Ghost3379/NX-ISD/ISD-Core/src/pins.h

#pragma once

// I2C
#define I2C_SDA 8
#define I2C_SCL 9

// SPI
#define SPI_SCK 40
#define SPI_MISO 41
#define SPI_MOSI 42

// Display 
#define CS_TFT 48
#define TFT_RS 21
#define TFT_RST 38
#define TFT_PWM 1
#define CS_SD 47

// Power Control
#define PWR_NPM 17

// Peripherals
#define NPM 18
#define BUZZER 10

// Buttons
#define BTN 13
#define LEVER_LEFT 16
#define LEVER_PUSH 15
#define LEVER_RIGHT 14

// Interrupts
#define INT_ALS 39
#define INT_RTC 6
#define INT_HR 5
#define INT_DOF 2
#define ALERT 4

// Charging & USB Detection
#define USB_DETECT 12
#define BAT_STAT 11
