Ghost3379/NX-ISD/ISD-Core/src/Watchface.h

#pragma once
#include <Arduino.h>
#include <LovyanGFX.hpp>
#include "SensorState.h"
#include "HAL.h"
#include "storage/StorageManager.h"

enum AppView {
  VIEW_NOTIFICATIONS = 0,
  VIEW_HOME          = 1,
  VIEW_QUICKPANEL    = 2
};

enum PowerAction {
  PWR_ACT_NONE = 0,
  PWR_ACT_STANDBY,
  PWR_ACT_SHUTDOWN,
  PWR_ACT_RESTART
};

class Watchface {
private:
  LGFX_Sprite canvas;
  bool initialized = false;

  // View state & animated transition
  AppView currentView = VIEW_HOME;
  AppView targetView  = VIEW_HOME;
  bool isTransitioning = false;
  uint32_t transitionStartTime = 0;
  int transitionDirection = 0; // +1 = moving right, -1 = moving left
  const uint32_t transitionDuration = 150; // 150ms snappy, responsive slide

  // TVA / Flipper Zero Amber-Orange Retro-Modern Palette
  uint16_t COLOR_BG;
  uint16_t COLOR_ORANGE_BRIGHT;
  uint16_t COLOR_ORANGE_MID;
  uint16_t COLOR_ORANGE_DIM;
  uint16_t COLOR_ORANGE_DARK;

  // Quickpanel Concept State
  int qpFocusIndex = 0;      // 0..5 focused tile
  bool qpInTileMode = false; // whether user is navigating inside the tiles
  bool qpEcoMode = false;
  NotificationMode qpNotifMode = NOTIF_SILENT;
  bool qpInNotifMenu = false;
  int notifMenuIndex = 0;
  bool qpHrmMeasuring = false;
  uint32_t qpHrmStartMs = 0;

  // Interactive Brightness Menu & Hardware Backlight State
  LGFX* display = nullptr;
  int brightnessPercent = 85;       // 10% .. 100%
  bool qpInBrightnessMenu = false;  // Active circular menu overlay

  // Interactive Power / Shutdown Menu State
  bool qpInShutdownMenu = false;    // Active power menu overlay
  int shutdownMenuIndex = 0;        // 0: Standby, 1: Shutdown, 2: Restart
  PowerAction requestedPowerAction = PWR_ACT_NONE;
  bool isStandby = false;           // Display off standby state
  bool needsFadeIn = false;        // Backlight fade-in trigger after wake frame push

  // Lever-Push Hold-to-Charge state for App Menu entrance
  uint32_t leverPushStartMs = 0;
  bool appMenuTriggered = false;
  bool settingsTriggered = false;
  float chargeProgress = 0.0f;

public:
  Watchface(LGFX* tft) : canvas(tft), display(tft) {}

  LGFX_Sprite* getCanvas() { return &canvas; }
  uint16_t getColorBg() const { return COLOR_BG; }
  uint16_t getColorOrangeBright() const { return COLOR_ORANGE_BRIGHT; }
  uint16_t getColorOrangeMid() const { return COLOR_ORANGE_MID; }
  uint16_t getColorOrangeDim() const { return COLOR_ORANGE_DIM; }
  uint16_t getColorOrangeDark() const { return COLOR_ORANGE_DARK; }

  bool checkAndClearAppMenuTrigger() {
    if (appMenuTriggered) {
      appMenuTriggered = false;
      return true;
    }
    return false;
  }

  bool checkAndClearSettingsTrigger() {
    if (settingsTriggered) {
      settingsTriggered = false;
      return true;
    }
    return false;
  }

  void playCyberTransition(bool toAppMenu, const SensorState& state) {
    if (!initialized || !display) return;

    // Keep outer technical frame and top status bar perfectly intact
    canvas.fillRect(4, 4, 232, 24, COLOR_BG);
    canvas.drawRect(4, 4, 232, 232, COLOR_ORANGE_DIM);
    canvas.drawFastHLine(4, 28, 232, COLOR_ORANGE_DIM);

    canvas.setTextSize(1);
    canvas.setTextColor(COLOR_ORANGE_MID, COLOR_BG);
    canvas.drawString("ISD-Core // ", 10, 10);
    canvas.setTextColor(COLOR_ORANGE_BRIGHT, COLOR_BG);
    canvas.drawString(toAppMenu ? "APP MENU" : "HOME", 82, 10);

    // Battery Readout
    char batBuf[16];
    if (state.batPercent > 0.0f) {
      int displayPct = (int)constrain(roundf(state.batPercent), 0.0f, 100.0f);
      if (state.usbConnected || state.isCharging) {
        snprintf(batBuf, sizeof(batBuf), "%d%% [CHG]", displayPct);
      } else {
        snprintf(batBuf, sizeof(batBuf), "%d%%", displayPct);
      }
      canvas.setTextColor(COLOR_ORANGE_BRIGHT, COLOR_BG);
    } else {
      snprintf(batBuf, sizeof(batBuf), "--%%");
      canvas.setTextColor(COLOR_ORANGE_DIM, COLOR_BG);
    }
    canvas.drawRightString(batBuf, 230, 10);

    // Clear viewport with a short subtle terminal lag
    canvas.fillRect(6, 29, 228, 203, COLOR_BG);

    display->startWrite();
    canvas.pushSprite(0, 0);
    display->endWrite();

    // Momentary tactical processing pause before target screen appears
    delay(75);
  }

  void applyBrightness() {
    HAL::applyBrightness(display);
  }

  int getBrightness() const {
    return HAL::brightnessPercent;
  }

  PowerAction getRequestedPowerAction() {
    PowerAction act = requestedPowerAction;
    requestedPowerAction = PWR_ACT_NONE;
    return act;
  }

  bool isInStandby() const {
    return isStandby;
  }

  void enterStandby() {
    isStandby = true;
    if (display) {
      HAL::fadeOutBacklight(display);
    }
  }

  void wakeFromStandby() {
    if (!isStandby) return;
    isStandby = false;
    currentView = VIEW_HOME;
    targetView = VIEW_HOME;
    isTransitioning = false;
    qpInTileMode = false;
    qpInBrightnessMenu = false;
    qpInShutdownMenu = false;
    qpInNotifMenu = false;
    if (HAL::backlightFadeMs > 0) {
      if (display) display->setBrightness(0);
      needsFadeIn = true;
    } else {
      applyBrightness();
    }
  }

  void setView(AppView v) {
    currentView = v;
    targetView = v;
    isTransitioning = false;
    qpInTileMode = false;
  }

  AppView getView() const {
    return isTransitioning ? targetView : currentView;
  }

  bool isAnimating() const {
    return isTransitioning || (leverPushStartMs > 0);
  }

  void startTransition(AppView target, int direction) {
    if (target == currentView && !isTransitioning) return;
    if (isTransitioning) {
      currentView = targetView;
    }
    targetView = target;
    transitionDirection = direction;
    transitionStartTime = millis();
    isTransitioning = true;
    qpInTileMode = false;
    qpFocusIndex = 0;
    qpInBrightnessMenu = false;
    qpInShutdownMenu = false;
    qpInNotifMenu = false;
  }

  void handleNavLeft() {
    if (isTransitioning) {
      isTransitioning = false;
      currentView = targetView;
    }
    if (currentView == VIEW_QUICKPANEL && qpInBrightnessMenu) {
      HAL::setBrightness(HAL::brightnessPercent + 5, display);
    } else if (currentView == VIEW_QUICKPANEL && qpInShutdownMenu) {
      shutdownMenuIndex = (shutdownMenuIndex + 2) % 3;
    } else if (currentView == VIEW_QUICKPANEL && qpInNotifMenu) {
      notifMenuIndex = (notifMenuIndex + 3) % 4;
    } else if (currentView == VIEW_QUICKPANEL && qpInTileMode) {
      qpFocusIndex = (qpFocusIndex + 5) % 6;
      HAL::buzzPip(3000, 10);
    } else if (currentView == VIEW_QUICKPANEL) {
      startTransition(VIEW_HOME, -1);
    } else if (currentView == VIEW_HOME) {
      startTransition(VIEW_NOTIFICATIONS, -1);
    }
  }

  void handleNavRight() {
    if (isTransitioning) {
      isTransitioning = false;
      currentView = targetView;
    }
    if (currentView == VIEW_QUICKPANEL && qpInBrightnessMenu) {
      HAL::setBrightness(HAL::brightnessPercent - 5, display);
    } else if (currentView == VIEW_QUICKPANEL && qpInShutdownMenu) {
      shutdownMenuIndex = (shutdownMenuIndex + 1) % 3;
    } else if (currentView == VIEW_QUICKPANEL && qpInNotifMenu) {
      notifMenuIndex = (notifMenuIndex + 1) % 4;
    } else if (currentView == VIEW_QUICKPANEL && qpInTileMode) {
      qpFocusIndex = (qpFocusIndex + 1) % 6;
      HAL::buzzPip(3000, 10);
    } else if (currentView == VIEW_NOTIFICATIONS) {
      startTransition(VIEW_HOME, 1);
    } else if (currentView == VIEW_HOME) {
      startTransition(VIEW_QUICKPANEL, 1);
    }
  }

  void handleNavPush() {
    if (isTransitioning) {
      isTransitioning = false;
      currentView = targetView;
    }
    if (currentView == VIEW_HOME) {
      // Lever push on Home is dedicated to the 2.0s hold charge gesture.
      // Quickpanel is accessed via lever right.
      return;
    } else if (currentView == VIEW_QUICKPANEL) {
      if (qpInShutdownMenu) {
        // Confirm and trigger selected power action
        switch (shutdownMenuIndex) {
          case 0:
            requestedPowerAction = PWR_ACT_STANDBY;
            break;
          case 1:
            // Shutdown functionality removed/disabled for now per user request
            requestedPowerAction = PWR_ACT_NONE;
            break;
          case 2:
            requestedPowerAction = PWR_ACT_RESTART;
            break;
        }
        qpInShutdownMenu = false;
      } else if (qpInBrightnessMenu) {
        // Exit circular brightness menu and confirm level
        qpInBrightnessMenu = false;
        StorageManager::extractConfigFromHAL(StorageManager::getActiveConfig());
        StorageManager::saveConfig(StorageManager::getActiveConfig());
      } else if (qpInNotifMenu) {
        qpNotifMode = (NotificationMode)notifMenuIndex;
        HAL::setNotificationMode(qpNotifMode);
        qpInNotifMenu = false;
        StorageManager::extractConfigFromHAL(StorageManager::getActiveConfig());
        StorageManager::saveConfig(StorageManager::getActiveConfig());
        if (!HAL::silentMode) {
          HAL::buzzPip(3500, 15);
        }
      } else if (!qpInTileMode) {
        // Enter tile navigation mode
        qpInTileMode = true;
        qpFocusIndex = 0;
        HAL::buzzPip(3500, 15);
      } else {
        // Toggle or activate the selected tile
        switch (qpFocusIndex) {
          case 0: // Settings
            settingsTriggered = true;
            HAL::buzzPip(3800, 15);
            break;
          case 1: // HRM
            qpHrmMeasuring = !qpHrmMeasuring;
            qpHrmStartMs = millis();
            break;
          case 2: // Eco Mode
            qpEcoMode = !qpEcoMode;
            HAL::ecoMode = qpEcoMode;
            StorageManager::extractConfigFromHAL(StorageManager::getActiveConfig());
            StorageManager::saveConfig(StorageManager::getActiveConfig());
            break;
          case 3: // Display / Brightness circular menu
            qpInBrightnessMenu = true;
            break;
          case 4: // Notification Methods Menu
            qpInNotifMenu = true;
            notifMenuIndex = (int)qpNotifMode;
            break;
          case 5: // Shutdown / Power Menu
            qpInShutdownMenu = true;
            shutdownMenuIndex = 0;
            break;
        }
      }
    } else if (currentView == VIEW_NOTIFICATIONS) {
      // Enter notifications
    }
  }

  void handleNavBack() {
    if (isTransitioning) {
      isTransitioning = false;
      currentView = targetView;
    }
    if (currentView == VIEW_QUICKPANEL) {
      if (qpInShutdownMenu) {
        qpInShutdownMenu = false;
      } else if (qpInBrightnessMenu) {
        qpInBrightnessMenu = false;
      } else if (qpInNotifMenu) {
        qpInNotifMenu = false;
      } else if (qpInTileMode) {
        qpInTileMode = false;
        HAL::buzzPip(2800, 10);
      } else {
        startTransition(VIEW_HOME, -1);
      }
    } else if (currentView == VIEW_NOTIFICATIONS) {
      startTransition(VIEW_HOME, 1);
    }
  }

  void handleNavSelect() {
    handleNavPush();
  }

  void begin() {
    canvas.setColorDepth(16); // 16-bit RGB565
    canvas.setPsram(true);    // Allocate in 8MB PSRAM for smooth double-buffering
    canvas.createSprite(240, 240);

    // Initialize Palette
    COLOR_BG            = canvas.color565(0, 0, 0);          // Pitch Black
    COLOR_ORANGE_BRIGHT = canvas.color565(255, 115, 0);      // High-vis vibrant amber
    COLOR_ORANGE_MID    = canvas.color565(190, 75, 0);       // Mid-tone orange
    COLOR_ORANGE_DIM    = canvas.color565(75, 28, 0);        // Dim hairline borders
    COLOR_ORANGE_DARK   = canvas.color565(35, 12, 0);        // Dark grid background

    applyBrightness();
    HAL::setNotificationMode(qpNotifMode);
    initialized = true;
  }

  void renderBootFrame(float progress) {
    canvas.fillScreen(COLOR_BG);

    // Big Bold NX-ISD Text (Size 4)
    canvas.setTextSize(4);
    canvas.setTextColor(COLOR_ORANGE_BRIGHT, COLOR_BG);
    canvas.drawCenterString("NX-ISD", 120, 68);

    // Thick Loading Bar
    const int barW = 160;
    const int barH = 10;
    const int barX = (240 - barW) / 2;
    const int barY = 120;

    // Track border & dark background
    canvas.drawRect(barX - 1, barY - 1, barW + 2, barH + 2, COLOR_ORANGE_DIM);
    canvas.fillRect(barX, barY, barW, barH, COLOR_ORANGE_DARK);

    // Progress Fill
    int fillW = (int)roundf(constrain(progress, 0.0f, 1.0f) * (float)barW);
    if (fillW > 0) {
      canvas.fillRect(barX, barY, fillW, barH, COLOR_ORANGE_BRIGHT);
    }

    // Version Tag Directly Under Loading Bar
    canvas.setTextSize(1);
    canvas.setTextColor(COLOR_ORANGE_MID, COLOR_BG);
    canvas.drawCenterString("v0p4", 120, 140);

    // Bottom Footer in the middle of the screen
    canvas.setTextSize(1);
    canvas.setTextColor(COLOR_ORANGE_DIM, COLOR_BG);
    canvas.drawCenterString("powered by ISD-Core", 120, 215);

    canvas.pushSprite(0, 0);
  }

  void playBootSequence(volatile float* hwProgress, volatile bool* hwDone, uint32_t minDurationMs = 1750) {
    if (!initialized) return;

    auto isInterrupted = [&]() -> bool {
      return (digitalRead(BTN) == LOW || digitalRead(LEVER_PUSH) == LOW ||
              digitalRead(LEVER_LEFT) == LOW || digitalRead(LEVER_RIGHT) == LOW);
    };

    uint32_t startMs = millis();
    float displayedProgress = 0.02f;

    while (true) {
      uint32_t now = millis();
      uint32_t elapsed = now - startMs;

      float currentHw = (hwProgress != nullptr) ? *hwProgress : 1.0f;
      bool done = (hwDone != nullptr) ? *hwDone : true;

      // Smoothly advance displayedProgress toward currentHw
      float diff = currentHw - displayedProgress;
      if (diff > 0.0f) {
        float step = diff * 0.08f;
        if (step < 0.003f) step = 0.003f;
        if (step > 0.015f) step = 0.015f; // Prevents abrupt jumps
        displayedProgress += step;
        if (displayedProgress > currentHw) displayedProgress = currentHw;
      }

      renderBootFrame(displayedProgress);

      // User interrupt: allow immediate skip only if background hardware bringup is complete
      if (isInterrupted() && done) {
        break;
      }

      // Check completion: hardware must be fully done, bar at 100%, and minimum duration met
      if (done && displayedProgress >= 0.995f && elapsed >= minDurationMs) {
        renderBootFrame(1.0f);
        delay(120); // Crisp final pause at 100%
        break;
      }

      delay(16); // ~60 FPS update rate
    }
  }

  void playBootAnimation() {
    float dummyHw = 1.0f;
    bool dummyDone = true;
    playBootSequence(&dummyHw, &dummyDone, 1750);
  }

  void render(const SensorState& state) {
    if (!initialized) return;

    // Check if lever push is held on Home watchface to charge into App Menu
    if (currentView == VIEW_HOME && !isTransitioning) {
      if (state.inputLeverPush) {
        if (leverPushStartMs == 0) {
          leverPushStartMs = millis();
        }
        uint32_t elapsed = millis() - leverPushStartMs;
        const uint32_t CHARGE_HOLD_DURATION_MS = 1200; // Snappy 1.2s charge
        chargeProgress = constrain((float)elapsed / (float)CHARGE_HOLD_DURATION_MS, 0.0f, 1.0f);
        if (elapsed >= CHARGE_HOLD_DURATION_MS) {
          appMenuTriggered = true;
          leverPushStartMs = 0;
          chargeProgress = 0.0f;
        }
      } else {
        leverPushStartMs = 0;
        chargeProgress = 0.0f;
      }
    } else {
      leverPushStartMs = 0;
      chargeProgress = 0.0f;
    }

    // Calculate transition interpolation with easeOutCubic curve
    int outgoingOffsetX = 0;
    int incomingOffsetX = 0;
    float dotX = 120.0f; // Center dot position

    if (isTransitioning) {
      uint32_t elapsed = millis() - transitionStartTime;
      if (elapsed >= transitionDuration) {
        isTransitioning = false;
        currentView = targetView;
      } else {
        float progress = (float)elapsed / (float)transitionDuration;
        // Cubic ease-out: 1 - (1 - t)^3
        float inv = 1.0f - progress;
        float eased = 1.0f - (inv * inv * inv);

        if (transitionDirection > 0) {
          // Navigating Right: Outgoing slides left (0 -> -240), Incoming slides from right (+240 -> 0)
          outgoingOffsetX = (int)(-eased * 240.0f);
          incomingOffsetX = outgoingOffsetX + 240;
        } else {
          // Navigating Left: Outgoing slides right (0 -> +240), Incoming slides from left (-240 -> 0)
          outgoingOffsetX = (int)(eased * 240.0f);
          incomingOffsetX = outgoingOffsetX - 240;
        }

        // Active dot track interpolation (108 -> 120 -> 132)
        float startDot = (currentView == VIEW_NOTIFICATIONS) ? 108.0f : (currentView == VIEW_HOME ? 120.0f : 132.0f);
        float endDot   = (targetView == VIEW_NOTIFICATIONS) ? 108.0f : (targetView == VIEW_HOME ? 120.0f : 132.0f);
        dotX = startDot + (endDot - startDot) * eased;
      }
    }

    if (!isTransitioning) {
      dotX = (currentView == VIEW_NOTIFICATIONS) ? 108.0f : (currentView == VIEW_HOME ? 120.0f : 132.0f);
    }

    // 1. Clear offscreen buffer to Pure Black
    canvas.fillScreen(COLOR_BG);

    // 2. View Content Area with Viewport Clipping (Y: 29 to 220)
    canvas.setClipRect(6, 29, 228, 192);
    if (isTransitioning) {
      renderViewContent(currentView, state, outgoingOffsetX);
      renderViewContent(targetView, state, incomingOffsetX);
    } else {
      renderViewContent(currentView, state, 0);
    }
    canvas.clearClipRect();

    // 3. Header Section (Title slides with subtle parallax, Battery stays fixed)
    renderHeader(state, outgoingOffsetX, incomingOffsetX);

    // 4. Outer Technical Border Framing
    canvas.drawRect(4, 4, 232, 232, COLOR_ORANGE_DIM);
    canvas.drawFastHLine(4, 28, 232, COLOR_ORANGE_DIM);

    // 5. Subtle Carousel Page Indicator with Smooth Gliding Active Dot
    renderPageIndicator(dotX);

    // 6. Flip Double Buffer to ST7789 (Zero Flicker)
    canvas.pushSprite(0, 0);

    if (needsFadeIn) {
      needsFadeIn = false;
      HAL::fadeInBacklight(display);
    }
  }

  void renderPowerMessage(const char* title, const char* subtitle, int iconType) {
    canvas.fillScreen(COLOR_BG);

    int cx = 120;
    int cy = 95;

    // Outer Avionic Frame
    canvas.drawRoundRect(16, 24, 208, 172, 10, COLOR_ORANGE_BRIGHT);
    canvas.drawRoundRect(18, 26, 204, 168, 8, COLOR_ORANGE_DARK);

    // Icon
    if (iconType == 1) { // Power off
      canvas.drawCircle(cx, cy - 20, 20, COLOR_ORANGE_BRIGHT);
      canvas.drawCircle(cx, cy - 20, 19, COLOR_ORANGE_BRIGHT);
      canvas.fillRect(cx - 5, cy - 42, 10, 8, COLOR_BG);
      canvas.fillRect(cx - 2, cy - 40, 4, 18, COLOR_ORANGE_BRIGHT);
    } else if (iconType == 2) { // Restart
      canvas.drawCircle(cx, cy - 20, 20, COLOR_ORANGE_BRIGHT);
      canvas.drawCircle(cx, cy - 20, 19, COLOR_ORANGE_BRIGHT);
      canvas.fillRect(cx, cy - 42, 18, 16, COLOR_BG);
      canvas.fillTriangle(cx + 12, cy - 42, cx + 22, cy - 20, cx + 6, cy - 25, COLOR_ORANGE_BRIGHT);
    }

    canvas.setTextSize(2);
    canvas.setTextColor(COLOR_ORANGE_BRIGHT, COLOR_BG);
    canvas.drawCenterString(title, cx, cy + 20);

    canvas.setTextSize(1);
    canvas.setTextColor(COLOR_ORANGE_MID, COLOR_BG);
    canvas.drawCenterString(subtitle, cx, cy + 50);

    // Direct flush to screen
    if (display) {
      display->startWrite();
      canvas.pushSprite(0, 0);
      display->endWrite();
    }
  }

private:
  const char* getViewTitle(AppView v) {
    if (v == VIEW_QUICKPANEL && qpInShutdownMenu) return "Power Menu";
    if (v == VIEW_QUICKPANEL && qpInBrightnessMenu) return "Brightness";
    switch (v) {
      case VIEW_NOTIFICATIONS: return "Notifications";
      case VIEW_QUICKPANEL:    return "Quickpanel";
      default:                 return "Home";
    }
  }

  void renderHeader(const SensorState& state, int outOffX, int inOffX) {
    canvas.setTextSize(1);

    // 1. Static Prefix: 'ISD-Core // ' stays locked in place
    canvas.setTextColor(COLOR_ORANGE_MID, COLOR_BG);
    canvas.drawString("ISD-Core // ", 10, 10);

    // 2. Dynamic Page Title Slot (starts at x=82, clipped so it never touches prefix or battery)
    canvas.setClipRect(82, 6, 85, 20);
    canvas.setTextColor(COLOR_ORANGE_BRIGHT, COLOR_BG);
    if (isTransitioning) {
      canvas.drawString(getViewTitle(currentView), 82 + (int)(outOffX * 0.4f), 10);
      canvas.drawString(getViewTitle(targetView), 82 + (int)(inOffX * 0.4f), 10);
    } else {
      canvas.drawString(getViewTitle(currentView), 82, 10);
    }
    canvas.clearClipRect();

    // Battery Readout (Rock solid at top right)
    char batBuf[16];
    if (state.batPercent > 0.0f) {
      int displayPct = (int)constrain(roundf(state.batPercent), 0.0f, 100.0f);
      if (state.usbConnected || state.isCharging) {
        snprintf(batBuf, sizeof(batBuf), "%d%% [CHG]", displayPct);
      } else {
        snprintf(batBuf, sizeof(batBuf), "%d%%", displayPct);
      }
      canvas.setTextColor(COLOR_ORANGE_BRIGHT, COLOR_BG);
    } else {
      snprintf(batBuf, sizeof(batBuf), "--%%");
      canvas.setTextColor(COLOR_ORANGE_DIM, COLOR_BG);
    }
    canvas.drawRightString(batBuf, 230, 10);
  }

  void renderViewContent(AppView view, const SensorState& state, int offsetX) {
    switch (view) {
      case VIEW_NOTIFICATIONS:
        renderNotifications(state, offsetX);
        break;
      case VIEW_HOME:
        renderHome(state, offsetX);
        break;
      case VIEW_QUICKPANEL:
        renderQuickpanel(state, offsetX);
        break;
    }
  }

  void renderHome(const SensorState& state, int offsetX) {
    // Clock Section
    const char* timeStr = (state.rtcTime[0] != '\0' && state.rtcTime[0] != '-') ? state.rtcTime : "--:--:--";
    canvas.setTextSize(3);
    canvas.setTextColor(COLOR_ORANGE_BRIGHT, COLOR_BG);
    canvas.drawCenterString(timeStr, 120 + offsetX, 44);

    // Date
    const char* dateStr = (state.rtcDate[0] != '\0' && state.rtcDate[0] != '-') ? state.rtcDate : "----/--/--";
    canvas.setTextSize(1);
    canvas.setTextColor(COLOR_ORANGE_MID, COLOR_BG);
    canvas.drawCenterString(dateStr, 120 + offsetX, 74);

    // Multipurpose Instrument Dial (Reticle + Spirit Level + Rotating Compass + Ambient Temp)
    int centerX = 120 + offsetX;
    int centerY = 152;
    int radius  = 40;

    // 1. Outer Dial Ring
    canvas.drawCircle(centerX, centerY, radius, COLOR_ORANGE_DIM);

    // 2. Subtle Reference Lines (avionic pitch / horizon rungs)
    canvas.drawFastHLine(centerX - 14, centerY - 14, 28, COLOR_ORANGE_DARK);
    canvas.drawFastHLine(centerX - 14, centerY + 14, 28, COLOR_ORANGE_DARK);

    // 3. Rotating Compass Axis with 'W' and 'E' Wings + North Indicator
    float headingRad = -1.5707963f; // Default North pointing UP (-90 deg)
    if (state.imuDataReady) {
      // Clockwise watch rotation decreases yaw, so (state.yaw - 90°) decreases angle (rotates counter-clockwise)
      // to keep pointing to true physical North!
      headingRad = (state.yaw - 90.0f) * 0.0174532925f;
    }

    // North angle, East angle (+90° CW), and West angle (+180° opposite East)
    float thetaN = headingRad;
    float thetaE = headingRad + 1.5707963f;
    float thetaW = thetaE + 3.14159265f;

    float cosE = cosf(thetaE);
    float sinE = sinf(thetaE);
    float cosW = -cosE;
    float sinW = -sinE;

    // A single continuous line through the middle from West wing to East wing (no arrow)
    int wx = centerX + (int)roundf(cosW * 52.0f);
    int wy = centerY + (int)roundf(sinW * 52.0f);
    int ex = centerX + (int)roundf(cosE * 52.0f);
    int ey = centerY + (int)roundf(sinE * 52.0f);

    // Draw the continuous line
    canvas.drawLine(wx, wy, ex, ey, COLOR_ORANGE_MID);

    // Cross-ticks at the wing ends (perpendicular to line, length 5 px)
    float perpX = -sinE * 2.5f;
    float perpY =  cosE * 2.5f;
    canvas.drawLine(wx - (int)perpX, wy - (int)perpY, wx + (int)perpX, wy + (int)perpY, COLOR_ORANGE_DIM);
    canvas.drawLine(ex - (int)perpX, ey - (int)perpY, ex + (int)perpX, ey + (int)perpY, COLOR_ORANGE_DIM);

    // 'W' and 'E' markings rotating dynamically with the wings
    int wLabelX = centerX + (int)roundf(cosW * 59.0f);
    int wLabelY = centerY + (int)roundf(sinW * 59.0f);
    int eLabelX = centerX + (int)roundf(cosE * 59.0f);
    int eLabelY = centerY + (int)roundf(sinE * 59.0f);

    canvas.setTextSize(1);
    canvas.setTextColor(COLOR_ORANGE_MID, COLOR_BG);
    canvas.drawCenterString("W", wLabelX, wLabelY - 3);
    canvas.drawCenterString("E", eLabelX, eLabelY - 3);

    // North Indicator: small prominent tick line crossing the circle rim where North is
    float cosN = cosf(thetaN);
    float sinN = sinf(thetaN);
    int nInX  = centerX + (int)roundf(cosN * 34.0f);
    int nInY  = centerY + (int)roundf(sinN * 34.0f);
    int nOutX = centerX + (int)roundf(cosN * 44.0f);
    int nOutY = centerY + (int)roundf(sinN * 44.0f);
    canvas.drawLine(nInX, nInY, nOutX, nOutY, COLOR_ORANGE_BRIGHT);

    // 4. Center Reference Hub / Level Target
    canvas.drawCircle(centerX, centerY, 5, COLOR_ORANGE_DARK);

    // 5. Active 2D Spirit Level Bubble (Aligned with 90° rotated display frame)
    if (state.imuDataReady) {
      // BNO085 axes mapped to screen rotation (tft.setRotation(3)):
      // Physical Left/Right tilt corresponds to pitch (inverted: -state.pitch -> Screen X)
      // Physical Forth/Back tilt corresponds to roll (-state.roll -> Screen Y)
      float bx = -state.pitch * 0.75f;
      float by = -state.roll * 0.75f;
      float dist = sqrtf(bx * bx + by * by);
      if (dist > 22.0f) {
        bx = (bx / dist) * 22.0f;
        by = (by / dist) * 22.0f;
      }
      int bubbleX = centerX + (int)roundf(bx);
      int bubbleY = centerY + (int)roundf(by);

      canvas.fillCircle(bubbleX, bubbleY, 3, COLOR_ORANGE_BRIGHT);
      canvas.drawCircle(bubbleX, bubbleY, 4, COLOR_ORANGE_MID);
    } else {
      canvas.fillCircle(centerX, centerY, 3, COLOR_ORANGE_MID);
    }

    // 6. Ambient Temperature Readout (Cleanly embedded in lower crescent of circle)
    char tempBuf[16];
    if (state.envDataReady && state.temp > -40.0f) {
      snprintf(tempBuf, sizeof(tempBuf), "%.1f", state.temp);
    } else {
      snprintf(tempBuf, sizeof(tempBuf), "--.-");
    }

    canvas.setTextSize(1);
    canvas.setTextColor(COLOR_ORANGE_MID, COLOR_BG);
    int tWidth = canvas.textWidth(tempBuf);
    int totalW = tWidth + 3 + 6; // number + gap + degree symbol (3) + 'C' (6)
    int startTx = centerX - totalW / 2;
    int textY = centerY + 22;

    canvas.drawString(tempBuf, startTx, textY);
    canvas.drawCircle(startTx + tWidth + 2, textY + 1, 1, COLOR_ORANGE_MID);
    canvas.drawString("C", startTx + tWidth + 5, textY);

    // 7. Tactical Compass Charge-Up (Hold LEVER_PUSH for 1.2s to enter App Menu)
    if (chargeProgress > 0.0f) {
      float sweepDeg = chargeProgress * 360.0f;
      // Denser and brighter outline right on the circle perimeter (radii 39, 40, 41)
      canvas.drawArc(centerX, centerY, 39, 41, -90.0f, -90.0f + sweepDeg, COLOR_ORANGE_BRIGHT);
      // Outer density glow at radius 42
      canvas.drawArc(centerX, centerY, 42, 42, -90.0f, -90.0f + sweepDeg, COLOR_ORANGE_MID);

      // Bright tracking charge node directly on the circle
      float headRad = (-90.0f + sweepDeg) * 0.0174532925f;
      int headX = centerX + (int)roundf(cosf(headRad) * 40.5f);
      int headY = centerY + (int)roundf(sinf(headRad) * 40.5f);
      canvas.fillCircle(headX, headY, 2, COLOR_ORANGE_BRIGHT);
    }
  }

  void renderNotifications(const SensorState& state, int offsetX) {
    canvas.setTextSize(1);
    canvas.setTextColor(COLOR_ORANGE_DIM, COLOR_BG);
    canvas.drawCenterString("NO NOTIFICATIONS", 120 + offsetX, 112);
    canvas.setTextColor(COLOR_ORANGE_DARK, COLOR_BG);
    canvas.drawCenterString("All caught up", 120 + offsetX, 130);
  }

  void renderQuickpanel(const SensorState& state, int offsetX) {
    canvas.setTextSize(1);

    // Dedicated Power / Shutdown Menu overlay
    if (qpInShutdownMenu) {
      renderShutdownMenu(offsetX);
      return;
    }

    // Dedicated Circular Brightness Menu overlay
    if (qpInBrightnessMenu) {
      renderBrightnessMenu(offsetX);
      return;
    }

    // Dedicated Notification Methods Menu overlay
    if (qpInNotifMenu) {
      renderNotifMenu(offsetX);
      return;
    }

    // 6 Concept Quick Action Tiles (Android Wear / Squircle Style)
    // Layout: 2 rows x 3 columns
    // Tile size: 64 x 62 px, corner radius: 8 px
    const int tileW = 64;
    const int tileH = 62;
    const int startX[3] = { 14, 88, 162 };
    const int startY[2] = { 46, 122 };

    char dispLabel[12];
    snprintf(dispLabel, sizeof(dispLabel), "%d%%", HAL::brightnessPercent);

    const char* notifTileLabels[4] = { "SILENT", "ALL", "SOUND", "LIGHTS" };
    const char* tileLabels[6] = {
      "SETTINGS",
      qpHrmMeasuring ? "MEASURE" : "HRM",
      qpEcoMode ? "ECO: ON" : "ECO: OFF",
      dispLabel,
      notifTileLabels[(int)qpNotifMode],
      "SHUTDOWN"
    };

    for (int i = 0; i < 6; i++) {
      int col = i % 3;
      int row = i / 3;
      int tx = startX[col] + offsetX;
      int ty = startY[row];
      int icx = tx + tileW / 2;
      int icy = ty + 22;

      bool isFocused = (qpInTileMode && qpFocusIndex == i);
      bool isToggledOn = false;
      if (i == 1 && qpHrmMeasuring) isToggledOn = true;
      if (i == 2 && qpEcoMode)      isToggledOn = true;
      if (i == 3 && brightnessPercent >= 90) isToggledOn = true;
      if (i == 4 && qpNotifMode != NOTIF_SILENT) isToggledOn = true;

      uint16_t borderColor = isFocused ? COLOR_ORANGE_BRIGHT : (isToggledOn ? COLOR_ORANGE_MID : COLOR_ORANGE_DIM);
      uint16_t iconColor   = isFocused ? COLOR_ORANGE_BRIGHT : (isToggledOn ? COLOR_ORANGE_BRIGHT : COLOR_ORANGE_MID);
      uint16_t textColor   = isFocused ? COLOR_ORANGE_BRIGHT : (isToggledOn ? COLOR_ORANGE_BRIGHT : COLOR_ORANGE_MID);

      // Background fill
      if (isToggledOn) {
        canvas.fillRoundRect(tx + 1, ty + 1, tileW - 2, tileH - 2, 7, COLOR_ORANGE_DARK);
      } else {
        canvas.fillRoundRect(tx + 1, ty + 1, tileW - 2, tileH - 2, 7, COLOR_BG);
      }

      // Border outline
      canvas.drawRoundRect(tx, ty, tileW, tileH, 8, borderColor);

      // High-vis focus halo / corner brackets
      if (isFocused) {
        canvas.drawRoundRect(tx - 2, ty - 2, tileW + 4, tileH + 4, 10, COLOR_ORANGE_BRIGHT);
      }

      // Vector Icon Rendering
      switch (i) {
        case 0: { // SETTINGS (Gear)
          canvas.drawCircle(icx, icy, 5, iconColor);
          canvas.fillCircle(icx, icy, 2, iconColor);
          for (int a = 0; a < 6; a++) {
            float rad = a * 1.04719755f;
            int x1 = icx + (int)roundf(cosf(rad) * 5.5f);
            int y1 = icy + (int)roundf(sinf(rad) * 5.5f);
            int x2 = icx + (int)roundf(cosf(rad) * 9.0f);
            int y2 = icy + (int)roundf(sinf(rad) * 9.0f);
            canvas.drawLine(x1, y1, x2, y2, iconColor);
          }
          break;
        }

        case 1: { // HRM (Heart with Pulse ECG Line)
          int heartR = 4;
          if (qpHrmMeasuring && ((millis() / 400) % 2 == 0)) {
            heartR = 5; // Beat pulse animation
          }
          canvas.fillCircle(icx - heartR, icy - 2, heartR, iconColor);
          canvas.fillCircle(icx + heartR, icy - 2, heartR, iconColor);
          canvas.fillTriangle(icx - (heartR * 2), icy, icx + (heartR * 2), icy, icx, icy + (heartR * 2), iconColor);
          // ECG cutout line
          canvas.drawLine(icx - 7, icy + 1, icx - 3, icy + 1, COLOR_BG);
          canvas.drawLine(icx - 3, icy + 1, icx - 1, icy - 4, COLOR_BG);
          canvas.drawLine(icx - 1, icy - 4, icx + 1, icy + 4, COLOR_BG);
          canvas.drawLine(icx + 1, icy + 4, icx + 3, icy + 1, COLOR_BG);
          canvas.drawLine(icx + 3, icy + 1, icx + 7, icy + 1, COLOR_BG);
          break;
        }

        case 2: { // ECO / POWER SAVE (Battery with Lightning Bolt)
          canvas.drawRoundRect(icx - 6, icy - 9, 12, 17, 2, iconColor);
          canvas.drawFastHLine(icx - 2, icy - 11, 4, iconColor);
          canvas.drawLine(icx + 1, icy - 6, icx - 2, icy - 1, iconColor);
          canvas.drawLine(icx - 2, icy - 1, icx + 2, icy - 1, iconColor);
          canvas.drawLine(icx + 2, icy - 1, icx - 1, icy + 5, iconColor);
          break;
        }

        case 3: { // DISPLAY (Sun / Brightness)
          canvas.drawCircle(icx, icy, 4, iconColor);
          canvas.fillCircle(icx, icy, 2, iconColor);
          for (int r = 0; r < 8; r++) {
            float rad = r * 0.785398f;
            int x1 = icx + (int)roundf(cosf(rad) * 6.0f);
            int y1 = icy + (int)roundf(sinf(rad) * 6.0f);
            int x2 = icx + (int)roundf(cosf(rad) * 9.5f);
            int y2 = icy + (int)roundf(sinf(rad) * 9.5f);
            canvas.drawLine(x1, y1, x2, y2, iconColor);
          }
          break;
        }

        case 4: { // NOTIFICATION METHOD (Bell with status accents)
          canvas.drawCircle(icx, icy - 2, 4, iconColor);
          canvas.drawLine(icx - 6, icy + 4, icx - 4, icy - 2, iconColor);
          canvas.drawLine(icx + 6, icy + 4, icx + 4, icy - 2, iconColor);
          canvas.drawFastHLine(icx - 7, icy + 4, 15, iconColor);
          canvas.fillCircle(icx, icy + 6, 1, iconColor);
          if (qpNotifMode == NOTIF_SILENT) {
            canvas.drawLine(icx - 8, icy - 8, icx + 8, icy + 8, COLOR_ORANGE_BRIGHT);
          } else if (qpNotifMode == NOTIF_ALL) {
            canvas.drawFastHLine(icx + 6, icy - 5, 3, COLOR_ORANGE_BRIGHT);
            canvas.drawFastVLine(icx + 7, icy - 6, 3, COLOR_ORANGE_BRIGHT);
          } else if (qpNotifMode == NOTIF_LIGHTS_ONLY) {
            canvas.drawFastVLine(icx, icy - 8, 3, COLOR_ORANGE_BRIGHT);
            canvas.drawFastHLine(icx - 9, icy, 3, COLOR_ORANGE_BRIGHT);
            canvas.drawFastHLine(icx + 7, icy, 3, COLOR_ORANGE_BRIGHT);
          }
          break;
        }

        case 5: { // POWER OFF / SHUTDOWN (Power Symbol)
          canvas.drawCircle(icx, icy + 1, 7, iconColor);
          canvas.fillRect(icx - 2, icy - 7, 5, 4, isToggledOn ? COLOR_ORANGE_DARK : COLOR_BG);
          canvas.drawFastVLine(icx, icy - 7, 8, iconColor);
          break;
        }
      }

      // Tile Label
      canvas.setTextColor(textColor, isToggledOn ? COLOR_ORANGE_DARK : COLOR_BG);
      canvas.drawCenterString(tileLabels[i], tx + tileW / 2, ty + 46);
    }

    // Bottom Navigation Context Bar
    canvas.setTextSize(1);
    canvas.setTextColor(COLOR_ORANGE_DIM, COLOR_BG);
    if (!qpInTileMode) {
      canvas.drawCenterString("PUSH LEVER TO NAVIGATE", 120 + offsetX, 196);
    } else {
      canvas.drawCenterString("LEVER: SELECT | BTN: BACK", 120 + offsetX, 196);
    }
  }

  void renderBrightnessMenu(int offsetX) {
    int cx = 120 + offsetX;
    int cy = 118;
    int radius = 62;

    // 1. Subtle Outer Reference Track Ring
    canvas.drawCircle(cx, cy, radius + 3, COLOR_ORANGE_DARK);
    canvas.drawCircle(cx, cy, radius - 11, COLOR_ORANGE_DARK);

    // 2. Technical Radial Ticks from 10% to 100% (19 ticks, spaced every 5%)
    // Angular sweep: 270 deg total, from 135 deg (bottom-left) to 405 deg (bottom-right)
    for (int p = 10; p <= 100; p += 5) {
      float frac = (p - 10) / 90.0f;
      float angleDeg = 135.0f + frac * 270.0f;
      float rad = angleDeg * 0.0174532925f;

      bool isMajor = (p % 10 == 0);
      float rIn = isMajor ? (radius - 10) : (radius - 5);
      float rOut = radius + 2;

      int x1 = cx + (int)roundf(cosf(rad) * rIn);
      int y1 = cy + (int)roundf(sinf(rad) * rIn);
      int x2 = cx + (int)roundf(cosf(rad) * rOut);
      int y2 = cy + (int)roundf(sinf(rad) * rOut);

      uint16_t tickColor = (p <= HAL::brightnessPercent) ? (isMajor ? COLOR_ORANGE_BRIGHT : COLOR_ORANGE_MID) : COLOR_ORANGE_DARK;
      canvas.drawLine(x1, y1, x2, y2, tickColor);
    }

    // 3. Active Orbital Satellite Pip (Glowing pointer pip outside the ring)
    float curFrac = (HAL::brightnessPercent - 10) / 90.0f;
    float curAngleDeg = 135.0f + curFrac * 270.0f;
    float curRad = curAngleDeg * 0.0174532925f;
    int pipX = cx + (int)roundf(cosf(curRad) * (radius + 9));
    int pipY = cy + (int)roundf(sinf(curRad) * (radius + 9));
    canvas.fillCircle(pipX, pipY, 3, COLOR_ORANGE_BRIGHT);
    canvas.drawCircle(pipX, pipY, 4, COLOR_ORANGE_MID);

    // 4. Central Sun Glyph
    int sunY = cy - 20;
    canvas.drawCircle(cx, sunY, 4, COLOR_ORANGE_BRIGHT);
    canvas.fillCircle(cx, sunY, 2, COLOR_ORANGE_BRIGHT);
    for (int r = 0; r < 8; r++) {
      float sRad = r * 0.785398f;
      int sx1 = cx + (int)roundf(cosf(sRad) * 6.0f);
      int sy1 = sunY + (int)roundf(sinf(sRad) * 6.0f);
      int sx2 = cx + (int)roundf(cosf(sRad) * 9.0f);
      int sy2 = sunY + (int)roundf(sinf(sRad) * 9.0f);
      canvas.drawLine(sx1, sy1, sx2, sy2, COLOR_ORANGE_MID);
    }

    // 5. Large Digital Readout
    canvas.setTextSize(3);
    canvas.setTextColor(COLOR_ORANGE_BRIGHT, COLOR_BG);
    char pBuf[8];
    snprintf(pBuf, sizeof(pBuf), "%d%%", HAL::brightnessPercent);
    canvas.drawCenterString(pBuf, cx, cy + 2);

    // 6. Context Bottom Bar
    canvas.setTextSize(1);
    canvas.setTextColor(COLOR_ORANGE_DIM, COLOR_BG);
    canvas.drawCenterString("< LEVER > ADJUST | PUSH: OK", cx, 196);
  }

  void renderShutdownMenu(int offsetX) {
    const char* titles[3] = { "STANDBY", "SHUTDOWN", "RESTART" };
    const char* descs[3]  = { "DISPLAY OFF (ANY KEY)", "DISABLED (PLANNED)", "REBOOT ISD-CORE" };

    int cardW = 216;
    int cardH = 46;
    int startX = 12 + offsetX;
    int startY[3] = { 44, 96, 148 };

    for (int i = 0; i < 3; i++) {
      bool isSelected = (i == shutdownMenuIndex);
      int cx = startX;
      int cy = startY[i];

      uint16_t cardBg = isSelected ? COLOR_ORANGE_DARK : COLOR_BG;
      uint16_t borderCol = isSelected ? COLOR_ORANGE_BRIGHT : COLOR_ORANGE_DIM;
      uint16_t textCol = isSelected ? COLOR_ORANGE_BRIGHT : COLOR_ORANGE_MID;
      uint16_t iconCol = isSelected ? COLOR_ORANGE_BRIGHT : COLOR_ORANGE_DIM;

      // Card Background & Border
      canvas.fillRoundRect(cx, cy, cardW, cardH, 8, cardBg);
      canvas.drawRoundRect(cx, cy, cardW, cardH, 8, borderCol);
      if (isSelected) {
        canvas.drawRoundRect(cx + 1, cy + 1, cardW - 2, cardH - 2, 7, borderCol);
        // Active indicator vertical bar on left edge
        canvas.fillRoundRect(cx + 4, cy + 8, 3, cardH - 16, 2, COLOR_ORANGE_BRIGHT);
      }

      // Card Icon
      int icx = cx + 24;
      int icy = cy + (cardH / 2);

      switch (i) {
        case 0: { // STANDBY (Crescent Moon)
          canvas.fillCircle(icx, icy, 8, iconCol);
          canvas.fillCircle(icx + 4, icy - 2, 6, cardBg);
          canvas.fillCircle(icx + 6, icy - 5, 1, iconCol);
          canvas.fillCircle(icx + 8, icy + 2, 1, iconCol);
          break;
        }
        case 1: { // SHUTDOWN (Power Symbol)
          canvas.drawCircle(icx, icy + 1, 8, iconCol);
          canvas.drawCircle(icx, icy + 1, 7, iconCol);
          canvas.fillRect(icx - 3, icy - 8, 6, 6, cardBg);
          canvas.fillRect(icx - 1, icy - 8, 3, 9, iconCol);
          break;
        }
        case 2: { // RESTART (Reboot circular arrow)
          canvas.drawCircle(icx, icy, 8, iconCol);
          canvas.drawCircle(icx, icy, 7, iconCol);
          canvas.fillRect(icx, icy - 10, 9, 8, cardBg);
          canvas.fillTriangle(icx + 6, icy - 10, icx + 9, icy - 2, icx + 2, icy - 5, iconCol);
          break;
        }
      }

      // Title & Subtitle
      canvas.setTextSize(2);
      canvas.setTextColor(textCol, cardBg);
      canvas.drawString(titles[i], cx + 46, cy + 7);

      canvas.setTextSize(1);
      canvas.setTextColor(isSelected ? COLOR_ORANGE_MID : COLOR_ORANGE_DIM, cardBg);
      canvas.drawString(descs[i], cx + 46, cy + 27);
    }

    // Bottom Navigation Context Prompt
    canvas.setTextSize(1);
    canvas.setTextColor(COLOR_ORANGE_DIM, COLOR_BG);
    canvas.drawCenterString("< LEVER > SELECT | PUSH: OK", 120 + offsetX, 206);
  }

  void renderNotifMenu(int offsetX) {
    const char* titles[4] = { "SILENT", "ALL", "SOUND ONLY", "LIGHTS ONLY" };
    const char* descs[4]  = { "MUTED BUZZER & LEDS", "BUZZER PIPS & MATRIX LED", "BUZZER PIPS ONLY", "SILENT MATRIX LED ONLY" };

    int cardW = 216;
    int cardH = 36;
    int startX = 12 + offsetX;
    int startY[4] = { 34, 74, 114, 154 };

    for (int i = 0; i < 4; i++) {
      bool isSelected = (i == notifMenuIndex);
      bool isCurrentActive = (i == (int)qpNotifMode);
      int cx = startX;
      int cy = startY[i];

      uint16_t cardBg = isSelected ? COLOR_ORANGE_DARK : COLOR_BG;
      uint16_t borderCol = isSelected ? COLOR_ORANGE_BRIGHT : (isCurrentActive ? COLOR_ORANGE_MID : COLOR_ORANGE_DIM);
      uint16_t textCol = isSelected ? COLOR_ORANGE_BRIGHT : COLOR_ORANGE_MID;
      uint16_t iconCol = isSelected ? COLOR_ORANGE_BRIGHT : (isCurrentActive ? COLOR_ORANGE_MID : COLOR_ORANGE_DIM);

      // Card Background & Border
      canvas.fillRoundRect(cx, cy, cardW, cardH, 6, cardBg);
      canvas.drawRoundRect(cx, cy, cardW, cardH, 6, borderCol);
      if (isSelected) {
        canvas.drawRoundRect(cx + 1, cy + 1, cardW - 2, cardH - 2, 5, borderCol);
        canvas.fillRoundRect(cx + 4, cy + 6, 3, cardH - 12, 2, COLOR_ORANGE_BRIGHT);
      }

      // Radio dot if currently active mode
      if (isCurrentActive) {
        int dotX = cx + cardW - 14;
        int dotY = cy + (cardH / 2);
        canvas.fillCircle(dotX, dotY, 3, COLOR_ORANGE_BRIGHT);
        canvas.drawCircle(dotX, dotY, 5, isSelected ? COLOR_ORANGE_BRIGHT : COLOR_ORANGE_MID);
      }

      // Card Icon
      int icx = cx + 22;
      int icy = cy + (cardH / 2);

      switch (i) {
        case 0: { // SILENT (Bell with Mute Slash)
          canvas.drawCircle(icx, icy - 2, 4, iconCol);
          canvas.drawLine(icx - 6, icy + 4, icx - 4, icy - 2, iconCol);
          canvas.drawLine(icx + 6, icy + 4, icx + 4, icy - 2, iconCol);
          canvas.drawFastHLine(icx - 7, icy + 4, 15, iconCol);
          canvas.fillCircle(icx, icy + 6, 1, iconCol);
          canvas.drawLine(icx - 7, icy - 7, icx + 7, icy + 7, COLOR_ORANGE_BRIGHT);
          break;
        }
        case 1: { // ALL (Bell with Sound & Light accents)
          canvas.drawCircle(icx - 2, icy - 2, 4, iconCol);
          canvas.drawLine(icx - 8, icy + 4, icx - 6, icy - 2, iconCol);
          canvas.drawLine(icx + 4, icy + 4, icx + 2, icy - 2, iconCol);
          canvas.drawFastHLine(icx - 9, icy + 4, 15, iconCol);
          canvas.fillCircle(icx - 2, icy + 6, 1, iconCol);
          canvas.drawFastHLine(icx + 6, icy - 3, 3, COLOR_ORANGE_BRIGHT);
          canvas.drawFastVLine(icx + 7, icy - 4, 3, COLOR_ORANGE_BRIGHT);
          canvas.drawFastHLine(icx + 6, icy + 3, 3, COLOR_ORANGE_MID);
          break;
        }
        case 2: { // SOUND ONLY (Bell with Sound Waves)
          canvas.drawCircle(icx - 2, icy - 2, 4, iconCol);
          canvas.drawLine(icx - 8, icy + 4, icx - 6, icy - 2, iconCol);
          canvas.drawLine(icx + 4, icy + 4, icx + 2, icy - 2, iconCol);
          canvas.drawFastHLine(icx - 9, icy + 4, 15, iconCol);
          canvas.fillCircle(icx - 2, icy + 6, 1, iconCol);
          canvas.drawCircle(icx + 2, icy - 2, 6, iconCol);
          canvas.fillRect(icx - 4, icy - 9, 6, 14, cardBg);
          break;
        }
        case 3: { // LIGHTS ONLY (Illuminated Rays)
          canvas.drawCircle(icx, icy, 5, iconCol);
          canvas.fillCircle(icx, icy, 2, iconCol);
          for (int r = 0; r < 6; r++) {
            float rad = r * 1.047197f;
            int x1 = icx + (int)roundf(cosf(rad) * 6.0f);
            int y1 = icy + (int)roundf(sinf(rad) * 6.0f);
            int x2 = icx + (int)roundf(cosf(rad) * 8.5f);
            int y2 = icy + (int)roundf(sinf(rad) * 8.5f);
            canvas.drawLine(x1, y1, x2, y2, iconCol);
          }
          break;
        }
      }

      // Title & Subtitle
      canvas.setTextSize(1);
      canvas.setTextColor(textCol, cardBg);
      canvas.drawString(titles[i], cx + 42, cy + 6, &fonts::Font2);

      canvas.setTextColor(isSelected ? COLOR_ORANGE_MID : COLOR_ORANGE_DIM, cardBg);
      canvas.drawString(descs[i], cx + 42, cy + 22);
    }

    // Context Prompt at bottom
    canvas.setTextSize(1);
    canvas.setTextColor(COLOR_ORANGE_DIM, COLOR_BG);
    canvas.drawCenterString("< LEVER > SELECT | PUSH: SET", 120 + offsetX, 198);
  }

  void renderPageIndicator(float dotX) {
    int y = 224;
    // Static base track
    canvas.drawCircle(108, y, 2, COLOR_ORANGE_DARK);
    canvas.drawCircle(120, y, 2, COLOR_ORANGE_DARK);
    canvas.drawCircle(132, y, 2, COLOR_ORANGE_DARK);

    // Smooth gliding active dot
    canvas.fillCircle((int)(dotX + 0.5f), y, 2, COLOR_ORANGE_BRIGHT);
  }
};
